waldbaer/1w-If/firmware/src/logging/logger.h

#ifndef OWIF_LOGGER_LOGGER_H
#define OWIF_LOGGER_LOGGER_H

// ---- Includes ----
#include <ArduinoLog.h>

#include <cstdint>

#include "logging/log_level.h"
#include "logging/status_led.h"

namespace owif {
namespace logging {

class Logger {
 public:
  Logger() = default;
  Logger(Logger const&) = default;
  Logger(Logger&&) = default;
  auto operator=(Logger const&) -> Logger& = default;
  auto operator=(Logger&&) -> Logger& = default;
  ~Logger() = default;

  // ---- Public APIs --------------------------------------------------------------------------------------------------

  auto Begin(Print& output_sink = Serial, LogLevel log_level = LogLevel::Info) -> bool;

  auto SetLogLevel(LogLevel log_level) -> void;
  auto GetLogLevel() -> LogLevel;

  template <class T, typename... Args>
  [[noreturn]] inline auto Abort(T msg, Args... args) -> void {
    std::uint8_t const led_flash_iterations{100};
    std::uint8_t const led_flash_on_duration{50};   // ms
    std::uint8_t const led_flash_off_duration{50};  // ms

    std::uint32_t const total_flash_duration{led_flash_iterations * (led_flash_on_duration + led_flash_off_duration) /
                                             1000};

    Fatal("%s", F("----------------------------------------------------------------------"));
    Fatal(F("Aborting further execution. Restarting in %usec..."), total_flash_duration);
    Fatal(F("Reason:"));
    Fatal(std::forward<T>(msg), std::forward<Args>(args)...);
    Fatal("%s", F("----------------------------------------------------------------------"));

    status_led_g.Flash(led_flash_iterations, led_flash_on_duration, led_flash_off_duration);
    status_led_g.Off();

    //  delay(5000);
    ESP.restart();
    while (true);
  }

  template <class T, typename... Args>
  inline auto Fatal(T msg, Args... args) -> void {
    Log.fatalln(std::forward<T>(msg), std::forward<Args>(args)...);
  }

  template <class T, typename... Args>
  inline auto FatalNoLn(T msg, Args... args) -> void {
    Log.fatal(std::forward<T>(msg), std::forward<Args>(args)...);
  }

  template <class T, typename... Args>
  inline auto Error(T msg, Args... args) -> void {
    Log.errorln(std::forward<T>(msg), std::forward<Args>(args)...);
  }

  template <class T, typename... Args>
  inline auto ErrorNoLn(T msg, Args... args) -> void {
    Log.error(std::forward<T>(msg), std::forward<Args>(args)...);
  }

  template <class T, typename... Args>
  inline auto Warn(T msg, Args... args) -> void {
    Log.warningln(std::forward<T>(msg), std::forward<Args>(args)...);
  }

  template <class T, typename... Args>
  inline auto WarnNoLn(T msg, Args... args) -> void {
    Log.warning(std::forward<T>(msg), std::forward<Args>(args)...);
  }

  template <class T, typename... Args>
  inline auto Info(T msg, Args... args) -> void {
    Log.infoln(std::forward<T>(msg), std::forward<Args>(args)...);
  }

  template <class T, typename... Args>
  inline auto InfoNoLn(T msg, Args... args) -> void {
    Log.info(std::forward<T>(msg), std::forward<Args>(args)...);
  }

  template <class T, typename... Args>
  inline auto Debug(T msg, Args... args) -> void {
    Log.traceln(std::forward<T>(msg), std::forward<Args>(args)...);
  }

  template <class T, typename... Args>
  inline auto DebugNoLn(T msg, Args... args) -> void {
    Log.trace(std::forward<T>(msg), std::forward<Args>(args)...);
  }

  template <class T, typename... Args>
  inline auto Verbose(T msg, Args... args) -> void {
    Log.verboseln(std::forward<T>(msg), std::forward<Args>(args)...);
  }

  template <class T, typename... Args>
  inline auto VerboseNoLn(T msg, Args... args) -> void {
    Log.verbose(std::forward<T>(msg), std::forward<Args>(args)...);
  }

 private:
  static auto PrintPrefix(Print* log_output, int log_level) -> void;
  static auto PrintTimestamp(Print* log_output) -> void;
  static auto PrintLogLevel(Print* log_output, int log_level) -> void;
};

/*!
 * \brief Declaration of global logger instance.
 */
extern Logger logger_g;

}  // namespace logging
}  // namespace owif

#endif  // OWIF_LOGGER_LOGGER_H
